BH4ME/sle_mesh_new/hardware/boards/sle-main-board/README.md

# SLE Main Board

这里保存 SLE 主板 PCB、预览图和可制造资料。

## Versions

- [v3.3](v3.3/)：2026-06-16 PCB PDF 和板卡预览图。
