BH4ME/sle_mesh_new/hardware/schematics/sle-main-board/README.md

# SLE Main Board Schematics

这里保存 SLE 主板原理图和硬件参考资料。

## Versions

- [v0.1](v0.1/)：2026-05-19 原理图参考 PDF。
- [v3.3](v3.3/)：2026-06-16 原理图 PDF。
