BH4ME/sle_mesh_new/hardware/enclosures/sle-pcb-enclosure/README.md

# SLE PCB Enclosure

SLE PCB enclosure 是给当前 WS63 SLE 板卡准备的 3D 打印外壳系列。版本目录中包含可打印 STL、可编辑/检查 STEP、预览图和生成源脚本。

## Versions

- [v1.1.4](v1.1.4/)：GPS 区域改为薄顶皮覆盖，保留 v1.1.3 的可打印配合改进。
