BH4ME/sle_mesh_new/hardware/schematics/sle-main-board/v3.3/README.md

# SLE Main Board Schematic v3.3

## 文件

- [SCH_Schematic1_3_2026-06-16.pdf](SCH_Schematic1_3_2026-06-16.pdf)
- [MANIFEST.md](MANIFEST.md)

## 用途

该 PDF 是 2026-06-16 导出的 SLE 主板 v3.3 原理图，用于硬件架构确认、接口核对和后续 PCB/固件联调参考。

对应 PCB 资料位于 [../../../boards/sle-main-board/v3.3](../../../boards/sle-main-board/v3.3/)。
