BH4ME/sle_mesh_new/hardware/schematics/sle-main-board/v0.1/README.md

# SLE Main Board Schematic v0.1

## 文件

- [SCH_Schematic1_2026-05-19.pdf](SCH_Schematic1_2026-05-19.pdf)

## 用途

该 PDF 是 V4 WS63/ST7789 引脚映射和硬件确认的参考资料。硬件资料统一放在 `hardware/schematics/` 下，避免散落在 `docs/` 或仓库根目录。
