BH4ME/sle_mesh_new/xc/ws63_team_network/sle_uart_server/sle_uart_server.h

/**
 * Copyright (c) HiSilicon (Shanghai) Technologies Co., Ltd. 2023-2023. All rights reserved.
 *
 * Description: SLE uart server Config. \n
 *
 * History: \n
 * 2023-07-17, Create file. \n
 */

#ifndef SLE_UART_SERVER_H
#define SLE_UART_SERVER_H

#include <stdint.h>
#include "sle_connection_manager.h"
#include "sle_device_discovery.h"
#include "sle_ssap_server.h"
#include "errcode.h"

#ifdef __cplusplus
#if __cplusplus
extern "C" {
#endif /* __cplusplus */
#endif /* __cplusplus */

/* Service UUID */
#define SLE_UUID_SERVER_SERVICE        0x2222

/* Property UUID */
#define SLE_UUID_SERVER_NTF_REPORT     0x2323

/* Property Property */
#define SLE_UUID_TEST_PROPERTIES  (SSAP_PERMISSION_READ | SSAP_PERMISSION_WRITE)

/* Operation indication */
#define SLE_UUID_TEST_OPERATION_INDICATION  (SSAP_OPERATE_INDICATION_BIT_READ | SSAP_OPERATE_INDICATION_BIT_WRITE)

/* Descriptor Property */
#define SLE_UUID_TEST_DESCRIPTOR   (SSAP_PERMISSION_READ | SSAP_PERMISSION_WRITE)

/* Server role bootstrap: SSAP service registration plus connectable advertising. */
errcode_t sle_uart_server_init(ssaps_read_request_callback ssaps_read_callback, ssaps_write_request_callback
    ssaps_write_callback);

errcode_t sle_uart_server_send_report_by_uuid(const uint8_t *data, uint8_t len);

/* Send helpers for leader/relay downstream packets. */
errcode_t sle_uart_server_send_report_by_handle(const uint8_t *data, uint16_t len);
errcode_t sle_uart_server_send_report_by_conn(uint16_t conn_id, const uint8_t *data, uint16_t len);

/* Map SDK connection IDs to logical member route IDs. */
uint8_t sle_uart_server_bind_member_conn(uint8_t member_id, uint16_t conn_id);
uint16_t sle_uart_server_find_conn_by_member(uint8_t member_id);
uint8_t sle_uart_server_find_conn_by_member_ex(uint8_t member_id, uint16_t *conn_id);
uint8_t sle_uart_server_has_conn(uint16_t conn_id);

/* SDK callback entry points forwarded by the app-level connection manager. */
void sle_uart_server_handle_connect_state_changed(uint16_t conn_id, const sle_addr_t *addr,
    sle_acb_state_t conn_state, sle_pair_state_t pair_state, sle_disc_reason_t disc_reason);
void sle_uart_server_handle_pair_complete(uint16_t conn_id, const sle_addr_t *addr, errcode_t status);
void sle_uart_server_handle_read_rssi(uint16_t conn_id, int8_t rssi, errcode_t status);

/* Diagnostics and connection-management helpers. */
uint16_t sle_uart_server_connected_count(void);
/* Backward-compatible alias, kept for existing call sites. */
uint16_t sle_uart_client_is_connected(void);
int8_t sle_uart_server_get_last_rssi(void);
errcode_t sle_uart_server_read_remote_rssi(void);
errcode_t sle_uart_server_disconnect_current(void);
uint8_t sle_uart_server_get_active_conns(uint16_t *conn_ids, uint8_t max_conns);
uint8_t sle_uart_server_get_conn_member(uint16_t conn_id, uint8_t *member_id);
uint8_t sle_uart_server_get_conn_rssi(uint16_t conn_id, int8_t *rssi);
errcode_t sle_uart_server_disconnect_conn(uint16_t conn_id);

typedef void (*sle_uart_server_msg_queue)(uint8_t *buffer_addr, uint16_t buffer_size);

void sle_uart_server_register_msg(sle_uart_server_msg_queue sle_uart_server_msg);


uint16_t get_connect_id(void);

#ifdef __cplusplus
#if __cplusplus
}
#endif /* __cplusplus */
#endif /* __cplusplus */

#endif
