BH4ME/sle_mesh_new/xc/ws63_team_network/sle_uart_server/sle_uart_server_adv.h

/**
 * Copyright (c) HiSilicon (Shanghai) Technologies Co., Ltd. 2023-2023. All rights reserved.
 *
 * Description: SLE ADV Config. \n
 *
 * History: \n
 * 2023-07-17, Create file. \n
 */

#ifndef SLE_SERVER_ADV_H
#define SLE_SERVER_ADV_H

#include <stdint.h>

#include "errcode.h"
#include "sle_common.h"
#include "sle_device_discovery.h"

typedef struct sle_adv_common_value {
    uint8_t type;
    uint8_t length;
    uint8_t value;
} le_adv_common_t;

typedef enum sle_adv_channel {
    SLE_ADV_CHANNEL_MAP_77                 = 0x01,
    SLE_ADV_CHANNEL_MAP_78                 = 0x02,
    SLE_ADV_CHANNEL_MAP_79                 = 0x04,
    SLE_ADV_CHANNEL_MAP_DEFAULT            = 0x07
} sle_adv_channel_map_t;

typedef enum sle_adv_data {
    SLE_ADV_DATA_TYPE_DISCOVERY_LEVEL                              = 0x01,   /* 发现等级 */
    SLE_ADV_DATA_TYPE_ACCESS_MODE                                  = 0x02,   /* 接入层能力 */
    SLE_ADV_DATA_TYPE_SERVICE_DATA_16BIT_UUID                      = 0x03,   /* 标准服务数据信息 */
    SLE_ADV_DATA_TYPE_SERVICE_DATA_128BIT_UUID                     = 0x04,   /* 自定义服务数据信息 */
    SLE_ADV_DATA_TYPE_COMPLETE_LIST_OF_16BIT_SERVICE_UUIDS         = 0x05,   /* 完整标准服务标识列表 */
    SLE_ADV_DATA_TYPE_COMPLETE_LIST_OF_128BIT_SERVICE_UUIDS        = 0x06,   /* 完整自定义服务标识列表 */
    SLE_ADV_DATA_TYPE_INCOMPLETE_LIST_OF_16BIT_SERVICE_UUIDS       = 0x07,   /* 部分标准服务标识列表 */
    SLE_ADV_DATA_TYPE_INCOMPLETE_LIST_OF_128BIT_SERVICE_UUIDS      = 0x08,   /* 部分自定义服务标识列表 */
    SLE_ADV_DATA_TYPE_SERVICE_STRUCTURE_HASH_VALUE                 = 0x09,   /* 服务结构散列值 */
    SLE_ADV_DATA_TYPE_SHORTENED_LOCAL_NAME                         = 0x0A,   /* 设备缩写本地名称 */
    SLE_ADV_DATA_TYPE_COMPLETE_LOCAL_NAME                          = 0x0B,   /* 设备完整本地名称 */
    SLE_ADV_DATA_TYPE_TX_POWER_LEVEL                               = 0x0C,   /* 广播发送功率 */
    SLE_ADV_DATA_TYPE_SLB_COMMUNICATION_DOMAIN                     = 0x0D,   /* SLB通信域域名 */
    SLE_ADV_DATA_TYPE_SLB_MEDIA_ACCESS_LAYER_ID                    = 0x0E,   /* SLB媒体接入层标识 */
    SLE_ADV_DATA_TYPE_EXTENDED                                     = 0xFE,   /* 数据类型扩展 */
    SLE_ADV_DATA_TYPE_MANUFACTURER_SPECIFIC_DATA                   = 0xFF    /* 厂商自定义信息 */
} sle_adv_data_type;

#define SLE_TEAM_ADV_ROUTE_MAGIC_0 0x53U
#define SLE_TEAM_ADV_ROUTE_MAGIC_1 0x4CU
#define SLE_TEAM_ADV_FW_COMPAT_ANY 0U

errcode_t sle_dev_register_cbks(void);

/* Metadata that is copied into the advertise/scan-response payload. */
void sle_uart_server_adv_set_local_addr(const uint8_t addr[SLE_ADDR_LEN]);
void sle_uart_server_adv_set_route_id(uint8_t route_id);
void sle_uart_server_adv_set_fw_compat(uint16_t fw_compat);

/* Advertiser lifecycle used by the server role. */
errcode_t sle_uart_server_adv_init(void);
errcode_t sle_uart_server_adv_restart(void);

/* Shared SDK announce/seek callback table merge for server and client roles. */
errcode_t sle_uart_announce_seek_merge_cbks(const sle_announce_seek_callbacks_t *cbks);

errcode_t sle_uart_announce_register_cbks(void);

#endif
