BH4ME/sle_mesh_new/automation/ws63/tools/ws63_multi_board_relay_recovery_test.py

#!/usr/bin/env python3
"""WS63 multi-board natural relay enrollment and recovery test."""

from __future__ import annotations

import argparse
import json
import pathlib
import re
import sys
import time
from typing import Iterable

try:
    from automation.ws63.tools import ws63_four_board_relay_test as fb
    from automation.ws63.tools import ws63_link_cycle_test as lc
    from automation.ws63.tools import ws63_natural_relay_leave_recovery_test as nr
except ModuleNotFoundError:  # pragma: no cover - direct script execution
    repo_root = pathlib.Path(__file__).resolve().parents[3]
    sys.path.insert(0, str(repo_root))
    from automation.ws63.tools import ws63_four_board_relay_test as fb
    from automation.ws63.tools import ws63_link_cycle_test as lc
    from automation.ws63.tools import ws63_natural_relay_leave_recovery_test as nr


def _progress(message: str) -> None:
    print(f"[multi-board] {message}", flush=True)


def _records_line(records: fb.MemberRecords, member_ids: Iterable[int]) -> str:
    parts: list[str] = []
    for member_id in member_ids:
        record = records.get(member_id, {})
        parts.append(
            f"{member_id}:online={record.get('online')} relay={record.get('relay')} "
            f"tier={record.get('tier')} last={record.get('last_seen')}"
        )
    return "; ".join(parts)


def _find_leader_crash_events(leader: lc.Peer, *, log_start: int) -> list[str]:
    text = "".join(leader.log[log_start:])
    crash_rx = re.compile(r"(APP\|exception:[0-9A-Fa-f]+|APP\|Oops:[^\r\n]*|APP\|Reboot core:[^\r\n]*)")
    boot_rx = re.compile(r"(device_main_init:\s*0!|\[team\] boot fw=[^\r\n]*|APP\|dbg uart init ok\.)")
    task_rx = re.compile(r"task:([^\r\n]+)")
    mepc_rx = re.compile(r"mepc:0x([0-9A-Fa-f]+)")
    events: list[str] = []
    for match in crash_rx.finditer(text):
        window = text[match.start() : min(len(text), match.start() + 700)]
        details = [match.group(1)]
        task_match = task_rx.search(window)
        mepc_match = mepc_rx.search(window)
        if task_match is not None:
            details.append(f"task={task_match.group(1).strip()}")
        if mepc_match is not None:
            details.append(f"mepc=0x{mepc_match.group(1)}")
        events.append(" ".join(details))
    for match in boot_rx.finditer(text):
        events.append(f"runtime leader boot marker: {match.group(1)}")
    return events


def _direct_members_from_topology(
    topology: dict[str, object],
    *,
    member_ids: Iterable[int],
    leader_id: int,
) -> list[int]:
    parent_by_member = topology.get("parent_by_member", {})
    direct_members: list[int] = []
    for member_id in member_ids:
        parent_id = nr._topology_int_lookup(parent_by_member, member_id)
        if parent_id == leader_id:
            direct_members.append(member_id)
    return direct_members


def _assert_runtime_invariants(
    leader: lc.Peer,
    topology: dict[str, object],
    *,
    member_ids: Iterable[int],
    leader_id: int,
    direct_cap: int,
    stage: str,
    leader_log_start: int,
) -> None:
    errors: list[str] = []
    crash_events = _find_leader_crash_events(leader, log_start=leader_log_start)
    if crash_events:
        errors.append("leader crash/reboot observed: " + "; ".join(crash_events[:4]))
    direct_members = _direct_members_from_topology(topology, member_ids=member_ids, leader_id=leader_id)
    if len(direct_members) > direct_cap:
        errors.append(f"direct_count={len(direct_members)} exceeds direct_cap={direct_cap}: {direct_members}")
    if errors:
        raise RuntimeError(f"{stage} runtime invariant failed: " + " | ".join(errors))


def _wait_stable_online(
    leader: lc.Peer,
    peers: list[lc.Peer],
    member_ids: list[int],
    *,
    seconds: float,
    poll_s: float,
) -> fb.MemberRecords:
    _progress(f"stability dwell {seconds:.0f}s: polling members")
    end = time.time() + seconds
    last: fb.MemberRecords = {}
    poll_count = 0
    while time.time() < end:
        records = fb._wait_member_records(
            leader,
            peers,
            expected={member_id: (1, None) for member_id in member_ids},
            timeout_s=10.0,
            poll_s=poll_s,
            note="stability all members online",
        )
        last = records
        poll_count += 1
        relays = fb._relay_ids_from_records(records, member_ids)
        _progress(f"stable poll {poll_count}: relays={relays}; {_records_line(records, member_ids)}")
        time.sleep(min(5.0, max(0.0, end - time.time())))
    return last


def _query_initial_statuses(
    peers: list[lc.Peer],
    *,
    expected_fw: str,
) -> dict[str, dict[str, object]]:
    statuses: dict[str, dict[str, object]] = {}
    for peer in peers:
        status = fb._query_cfg(peer, peers, window_s=3.0, attempts=5)
        fw = status.get("fw")
        if expected_fw and fw != expected_fw:
            raise RuntimeError(f"{peer.name} firmware mismatch: expected {expected_fw}, got {fw}")
        statuses[peer.name] = status
        _progress(
            f"{peer.name} {peer.port}: fw={fw} suffix={status.get('selfSuffix')} "
            f"route={status.get('routeId')} role={status.get('runtimeRole')}"
        )
    return statuses


def run(args: argparse.Namespace) -> int:
    peers: list[lc.Peer] = []
    leader_id: int | None = None
    log_dir = pathlib.Path(args.log_dir)
    summary_path = log_dir / "summary.json"
    summary: dict[str, object] = {
        "leader_port": args.leader_port,
        "member_ports": args.member_ports,
        "expected_fw": args.expected_fw,
        "team_id": args.team_id,
        "channel": args.channel,
        "direct_cap": args.direct_cap,
        "relay_target": args.relay_target,
        "log_dir": str(log_dir),
    }
    try:
        if len(args.member_ports) < 2:
            raise RuntimeError("at least two member ports are required to exercise relay failover")

        log_dir.mkdir(parents=True, exist_ok=True)
        leader = lc._open_peer("leader", args.leader_port, args.baudrate)
        members = [
            lc._open_peer(f"member{idx}", port, args.baudrate)
            for idx, port in enumerate(args.member_ports, start=1)
        ]
        peers = [leader, *members]

        _progress("drain serial boot logs")
        fb._drain_all(peers, args.initial_drain_s)

        statuses = _query_initial_statuses(peers, expected_fw=args.expected_fw)
        summary["initial_statuses"] = statuses
        leader_suffix = str(statuses["leader"].get("selfSuffix"))
        leader_id = int(statuses["leader"].get("routeId"))
        member_ids = [int(statuses[member.name].get("routeId")) for member in members]
        peer_by_id = {member_id: peer for member_id, peer in zip(member_ids, members)}
        all_route_ids = [leader_id, *member_ids]
        if len(set(all_route_ids)) != len(all_route_ids):
            raise RuntimeError(f"route ids must be unique: {all_route_ids}")
        summary["leader_id"] = leader_id
        summary["member_ids"] = member_ids

        if not args.no_clean_start:
            fb._clean_start_saved_config(
                peers,
                timeout_s=args.cmd_timeout_s,
                boot_timeout_s=args.boot_timeout_s,
                reboot_command=args.reboot_command,
            )
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
